wieslawsoltes/CrystalBall/mechanical/step/REF_mic_module.step

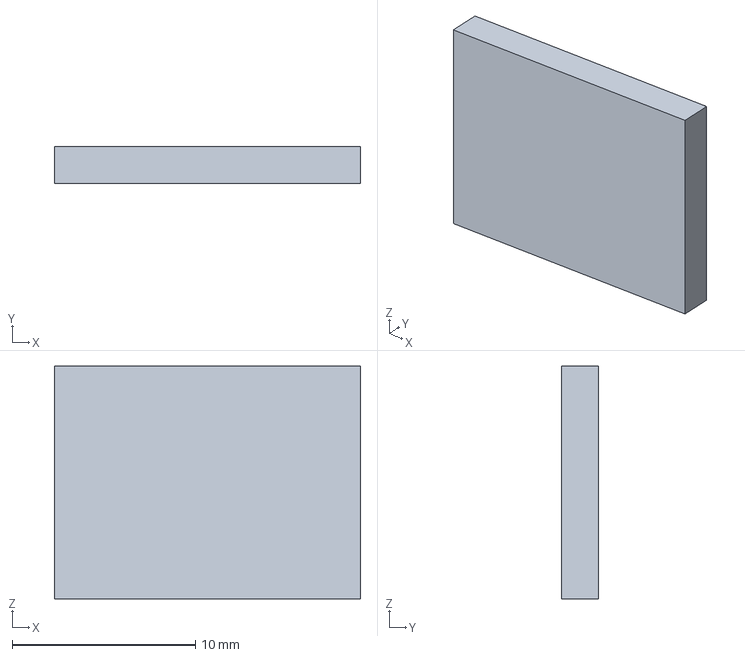
[picture p17: CAD file, 2026-09-16]
mechanical/step/REF_mic_module.step
16.7 x 2.00 x 12.7 mm
