wieslawsoltes/CrystalBall/mechanical/step/06_globe_gasket.step

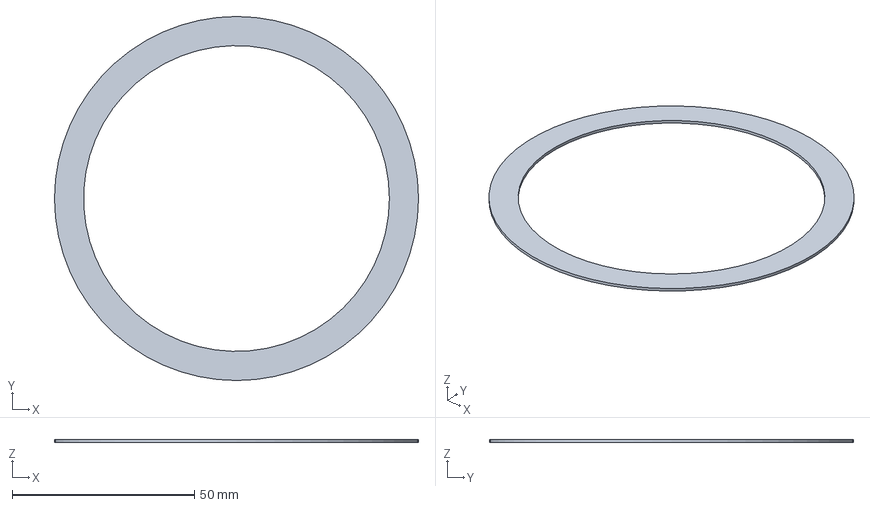
[picture p18: CAD file, 2026-09-16]
mechanical/step/06_globe_gasket.step
100.0 x 100.0 x 0.8 mm
