wieslawsoltes/CrystalBall/mechanical/step/05_globe_bond_flange.step

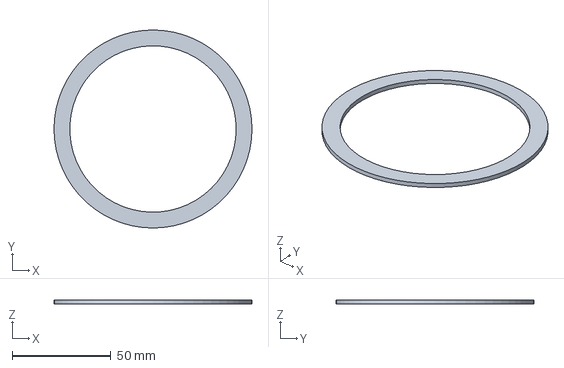
[picture p19: CAD file, 2026-09-16]
mechanical/step/05_globe_bond_flange.step
100.0 x 100.0 x 2.00 mm
