wieslawsoltes/CrystalBall/mechanical/step/REF_LCD_active.step

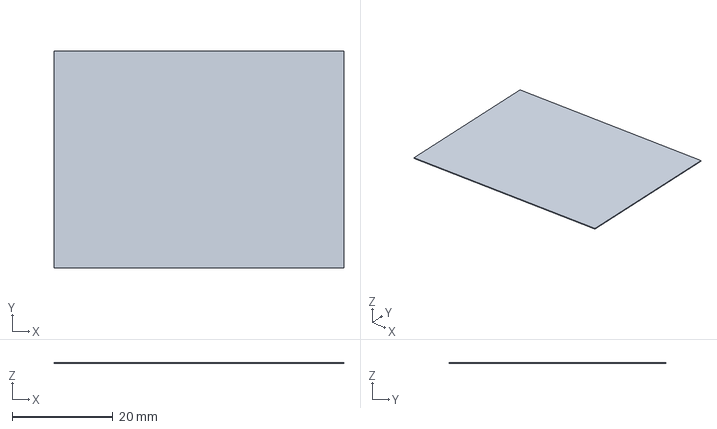
[picture p20: CAD file, 2026-09-16]
mechanical/step/REF_LCD_active.step
57.6 x 43.2 x 0.2 mm
