wieslawsoltes/CrystalBall/mechanical/step/18_microphone_clip.step

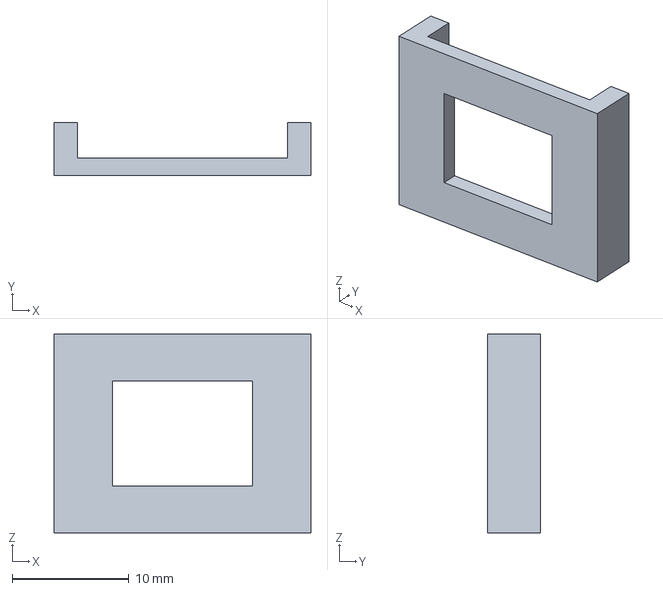
[picture p21: CAD file, 2026-09-16]
mechanical/step/18_microphone_clip.step
22.0 x 4.50 x 17.0 mm
