wieslawsoltes/CrystalBall/mechanical/step/REF_amp_module.step

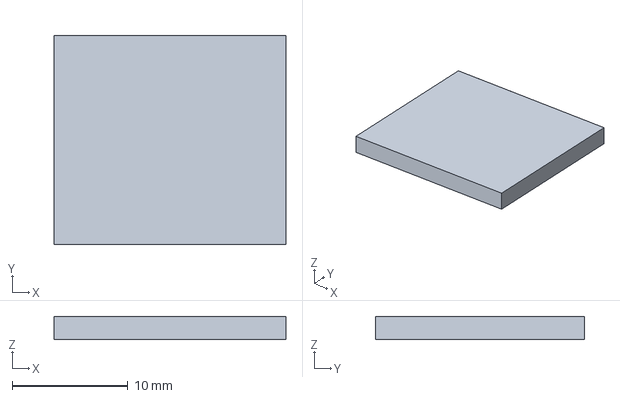
[picture p22: CAD file, 2026-09-16]
mechanical/step/REF_amp_module.step
20.0 x 18.0 x 2.00 mm
