wieslawsoltes/CrystalBall/mechanical/step/09_mirror_frame.step

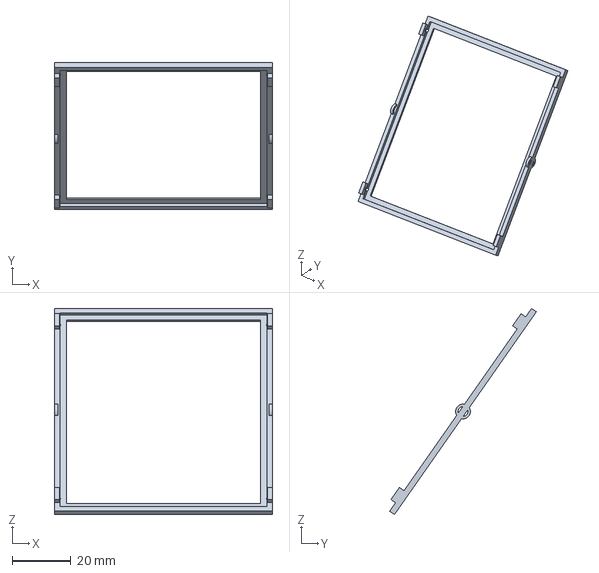
[picture p23: CAD file, 2026-09-16]
mechanical/step/09_mirror_frame.step
74.0 x 49.8 x 70.0 mm
