wieslawsoltes/CrystalBall/mechanical/step/REF_LCD_1770.step

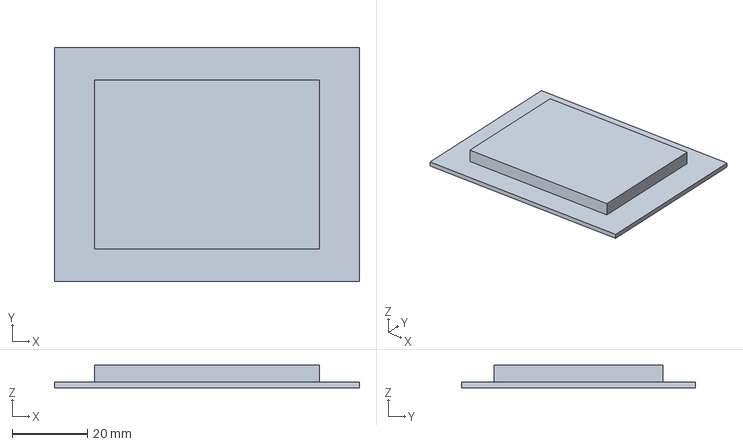
[picture p24: CAD file, 2026-09-16]
mechanical/step/REF_LCD_1770.step
81.3 x 62.5 x 6.10 mm
