wieslawsoltes/CrystalBall/mechanical/step/REF_carrier_PCB.step

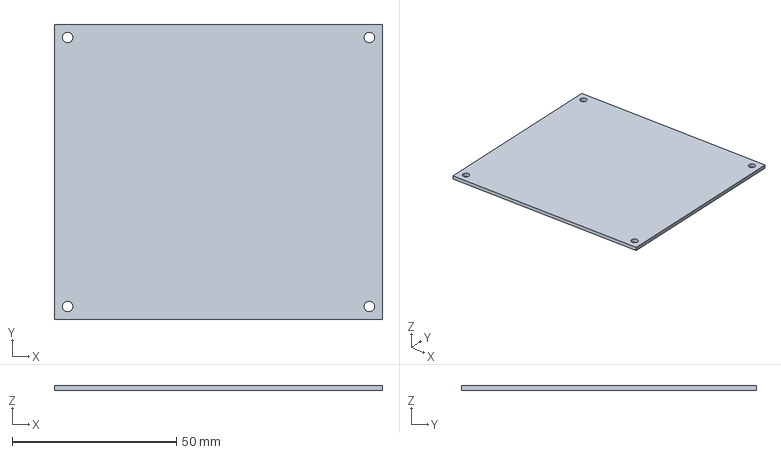
[picture p25: CAD file, 2026-09-16]
mechanical/step/REF_carrier_PCB.step
100.0 x 90.0 x 1.60 mm
