wieslawsoltes/CrystalBall/mechanical/step/10_mirror_retainer.step

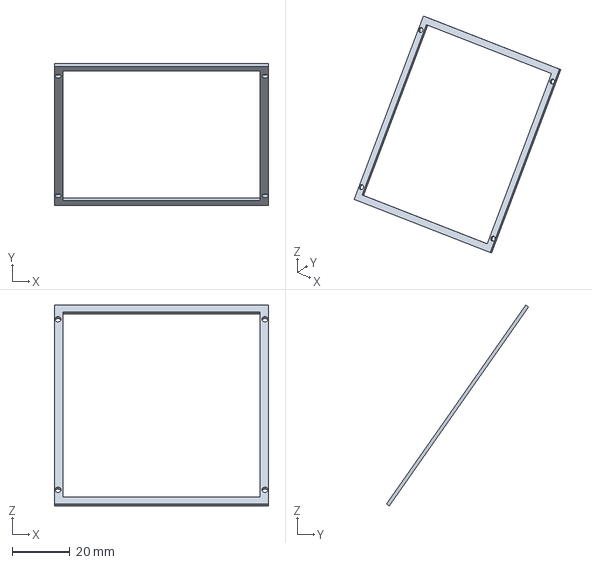
[picture p26: CAD file, 2026-09-16]
mechanical/step/10_mirror_retainer.step
74.0 x 49.2 x 69.5 mm
