wieslawsoltes/CrystalBall/mechanical/step/13_halo_rail.step

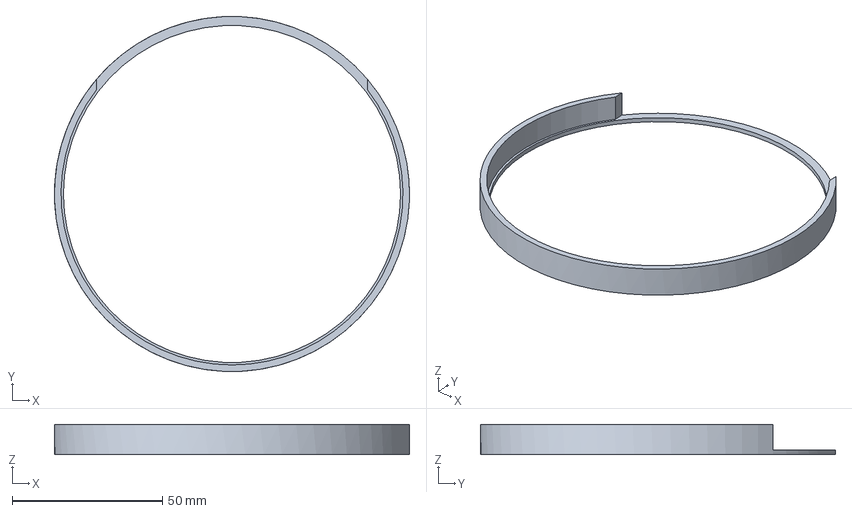
[picture p27: CAD file, 2026-09-16]
mechanical/step/13_halo_rail.step
117.9 x 117.9 x 10.0 mm
