wieslawsoltes/CrystalBall/mechanical/step/16_pd_module_sled.step

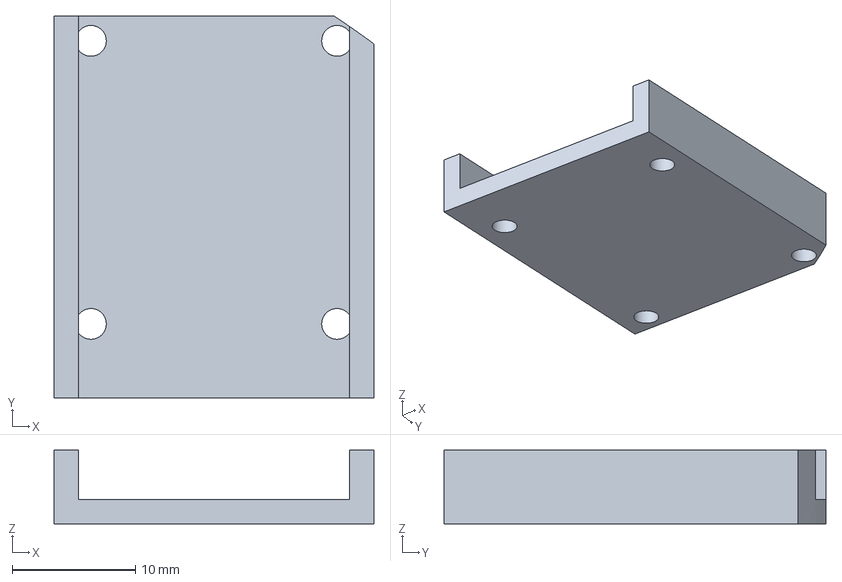
[picture p28: CAD file, 2026-09-16]
mechanical/step/16_pd_module_sled.step
26.0 x 31.0 x 6.00 mm
