wieslawsoltes/CrystalBall/mechanical/step/17_fit_coupon.step

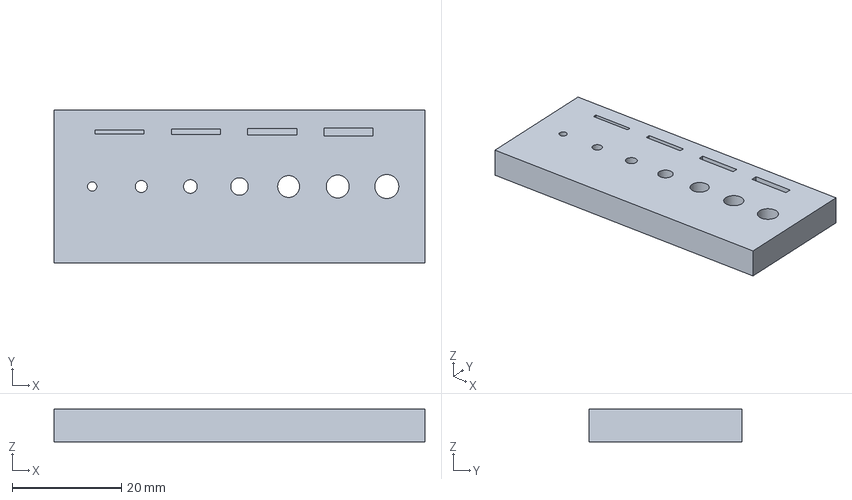
[picture p29: CAD file, 2026-09-16]
mechanical/step/17_fit_coupon.step
68.0 x 28.0 x 6.00 mm
