wieslawsoltes/CrystalBall/mechanical/step/02_bottom_cover.step

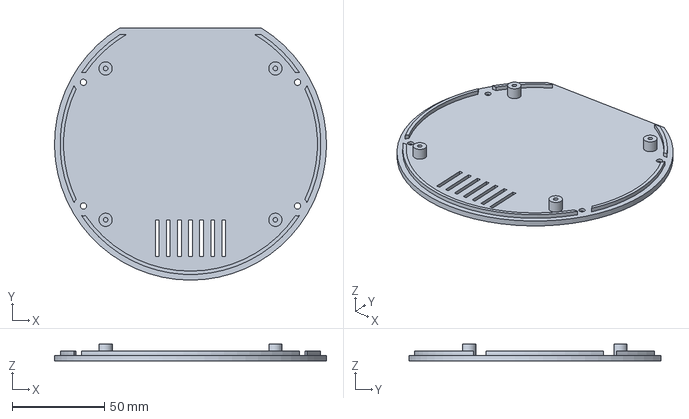
[picture p30: CAD file, 2026-09-16]
mechanical/step/02_bottom_cover.step
147.4 x 136.7 x 9.00 mm
