wieslawsoltes/CrystalBall/mechanical/step/01_base_shell.step

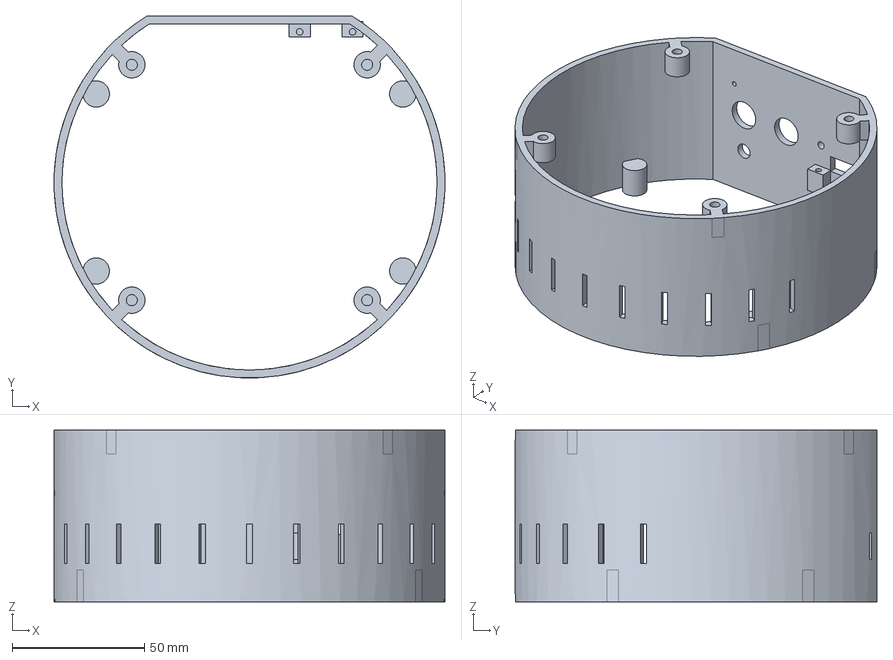
[picture p31: CAD file, 2026-09-16]
mechanical/step/01_base_shell.step
148.0 x 137.0 x 65.0 mm
