wieslawsoltes/CrystalBall/mechanical/step/04_optical_globe.step

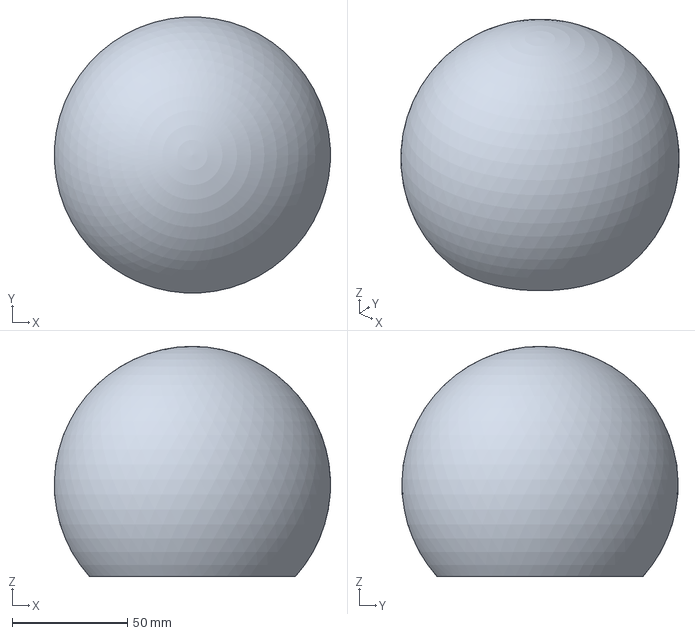
[picture p32: CAD file, 2026-09-16]
mechanical/step/04_optical_globe.step
119.8 x 119.7 x 100.0 mm
