wieslawsoltes/CrystalBall/mechanical/step/11_beamsplitter_OPTICAL.step

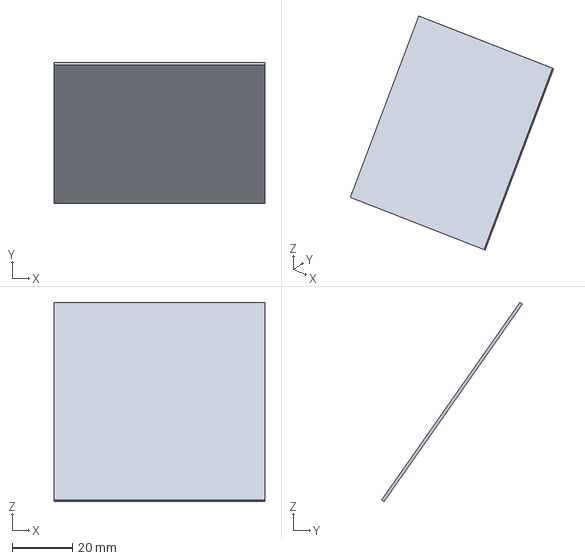
[picture p33: CAD file, 2026-09-16]
mechanical/step/11_beamsplitter_OPTICAL.step
70.0 x 46.7 x 66.1 mm
