wieslawsoltes/CrystalBall/verification/pages/mobile.png

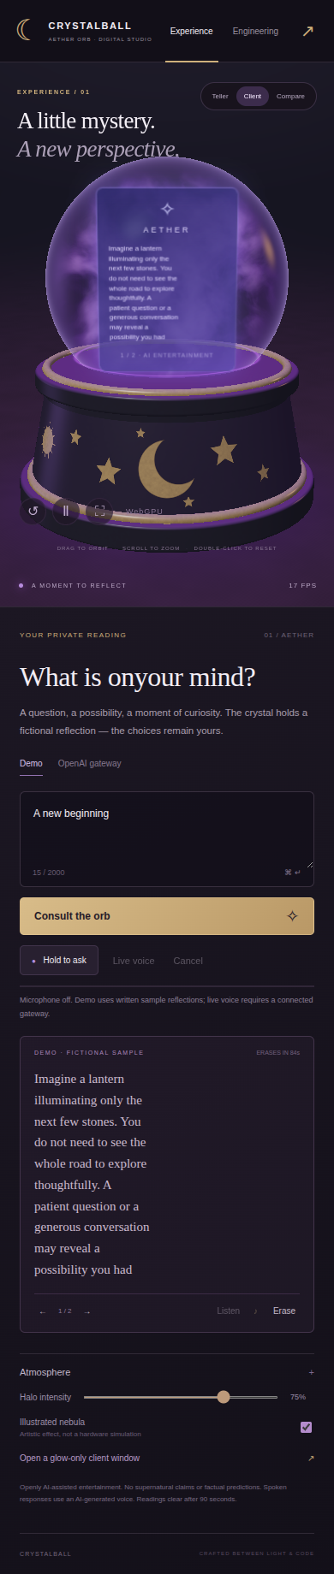
verification/pages/mobile.png
