wieslawsoltes/CrystalBall/firmware/main/glyphs.h

#pragma once
// Original 5x7 uppercase bitmap glyphs. Lowercase is rendered uppercase.
static const unsigned char orb_glyphs[96][7] = {
 {0,0,0,0,0,0,0}, // 32
 {4,4,4,4,4,0,4}, // 33
 {10,10,0,0,0,0,0}, // 34
 {14,17,1,2,4,0,4}, // 35
 {14,17,1,2,4,0,4}, // 36
 {25,26,2,4,8,11,19}, // 37
 {14,17,1,2,4,0,4}, // 38
 {4,4,8,0,0,0,0}, // 39
 {2,4,8,8,8,4,2}, // 40
 {8,4,2,2,2,4,8}, // 41
 {14,17,1,2,4,0,4}, // 42
 {0,4,4,31,4,4,0}, // 43
 {0,0,0,0,0,4,8}, // 44
 {0,0,0,31,0,0,0}, // 45
 {0,0,0,0,0,0,4}, // 46
 {1,1,2,4,8,16,16}, // 47
 {14,17,19,21,25,17,14}, // 48
 {4,12,4,4,4,4,14}, // 49
 {14,17,1,2,4,8,31}, // 50
 {30,1,1,14,1,1,30}, // 51
 {2,6,10,18,31,2,2}, // 52
 {31,16,16,30,1,1,30}, // 53
 {14,16,16,30,17,17,14}, // 54
 {31,1,2,4,8,8,8}, // 55
 {14,17,17,14,17,17,14}, // 56
 {14,17,17,15,1,1,14}, // 57
 {0,4,0,0,4,0,0}, // 58
 {0,4,0,0,4,4,8}, // 59
 {14,17,1,2,4,0,4}, // 60
 {0,0,31,0,31,0,0}, // 61
 {14,17,1,2,4,0,4}, // 62
 {14,17,1,2,4,0,4}, // 63
 {14,17,1,2,4,0,4}, // 64
 {14,17,17,31,17,17,17}, // 65
 {30,17,17,30,17,17,30}, // 66
 {15,16,16,16,16,16,15}, // 67
 {30,17,17,17,17,17,30}, // 68
 {31,16,16,30,16,16,31}, // 69
 {31,16,16,30,16,16,16}, // 70
 {15,16,16,23,17,17,14}, // 71
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
};
