wieslawsoltes/CrystalBall/tools/stroke.py

"""Small, original 5x7 bitmap lettering, emitted as line segments for fabrication text."""
PATTERNS={
'A':['01110','10001','10001','11111','10001','10001','10001'],
'B':['11110','10001','10001','11110','10001','10001','11110'],
'C':['01111','10000','10000','10000','10000','10000','01111'],
'D':['11110','10001','10001','10001','10001','10001','11110'],
'E':['11111','10000','10000','11110','10000','10000','11111'],
'F':['11111','10000','10000','11110','10000','10000','10000'],
'G':['01111','10000','10000','10111','10001','10001','01110'],
'H':['10001','10001','10001','11111','10001','10001','10001'],
'I':['11111','00100','00100','00100','00100','00100','11111'],
'J':['00111','00010','00010','00010','10010','10010','01100'],
'K':['10001','10010','10100','11000','10100','10010','10001'],
'L':['10000','10000','10000','10000','10000','10000','11111'],
'M':['10001','11011','10101','10101','10001','10001','10001'],
'N':['10001','11001','10101','10011','10001','10001','10001'],
'O':['01110','10001','10001','10001','10001','10001','01110'],
'P':['11110','10001','10001','11110','10000','10000','10000'],
'Q':['01110','10001','10001','10001','10101','10010','01101'],
'R':['11110','10001','10001','11110','10100','10010','10001'],
'S':['01111','10000','10000','01110','00001','00001','11110'],
'T':['11111','00100','00100','00100','00100','00100','00100'],
'U':['10001','10001','10001','10001','10001','10001','01110'],
'V':['10001','10001','10001','10001','10001','01010','00100'],
'W':['10001','10001','10001','10101','10101','10101','01010'],
'X':['10001','10001','01010','00100','01010','10001','10001'],
'Y':['10001','10001','01010','00100','00100','00100','00100'],
'Z':['11111','00001','00010','00100','01000','10000','11111'],
'0':['01110','10001','10011','10101','11001','10001','01110'],
'1':['00100','01100','00100','00100','00100','00100','01110'],
'2':['01110','10001','00001','00010','00100','01000','11111'],
'3':['11110','00001','00001','01110','00001','00001','11110'],
'4':['00010','00110','01010','10010','11111','00010','00010'],
'5':['11111','10000','10000','11110','00001','00001','11110'],
'6':['01110','10000','10000','11110','10001','10001','01110'],
'7':['11111','00001','00010','00100','01000','01000','01000'],
'8':['01110','10001','10001','01110','10001','10001','01110'],
'9':['01110','10001','10001','01111','00001','00001','01110'],
'.':['00000']*6+['00100'],',':['00000']*5+['00100','01000'],
':':['00000','00100','00000','00000','00100','00000','00000'],
';':['00000','00100','00000','00000','00100','00100','01000'],
'-':['00000']*3+['11111']+['00000']*3,
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
}
def text_lines(text,x,y,size):
    unit=size/7;out=[]
    for i,ch in enumerate(text.upper()):
        for r,row in enumerate(PATTERNS.get(ch,PATTERNS['?'])):
            for c,v in enumerate(row):
                if v=='1':
                    xx=x+(i*6+c)*unit;yy=y+r*unit
                    out.append((max(.10,unit*.8),(xx,yy),(xx+unit*.30,yy)))
    return out
if __name__=='__main__':
    from pathlib import Path
    root=Path(__file__).resolve().parents[1]
    s=['#pragma once','// Original 5x7 uppercase bitmap glyphs. Lowercase is rendered uppercase.','static const unsigned char orb_glyphs[96][7] = {']
    for i in range(32,128):
        p=PATTERNS.get(chr(i).upper(),PATTERNS['?'])
        s.append(' {'+','.join(str(int(row,2)) for row in p)+'}, // '+str(i))
    s.append('};');(root/'firmware/main/glyphs.h').write_text('\n'.join(s)+'\n')
